bcancinov/mdc-power-p6/sim/p6.asc

@1: fra; delay=1m fstart=1.875K fend=480K oct=2 fcoarse=15K pp0=192m pp1=12m f0=1.875K f1=30K tavgmin=50µ tsettle=33.3333µ
C1: cap; 0.1µ
C2: cap; 1µF
C3: cap; 22µ; Rser=40m Lser=1.7n
C4: cap; 100µ; Rser=80m Lser=3n
C5: cap; 10µ; Rser=3m Lser=0.5n
Coc1: cap; 39.162µ; x4; Rser=2.17m Lser=0.2n
Cth1: cap; 10n
Cthp1: cap; 180p
E1: e; 1
E2: e; 1
R1: res; 10.7k
R2: res; 1k
R3: res; 100k
R4: res; '6/0.01'
R5: res; 0.5
R6: res; 0.22
R7: res; '6/3'
Rfreq1: res; 47k
Riset1: res; 60.4k
Rth1: res; 1.33k
U1: LT8624S
U2: XGL4020
U3: XGL4020
Vin1: voltage; 12V
Named nets: 0, SW, PGFB, SET, VOUT1, VLDO, out1, out2
LT8624S - 18V, 4A Synchronous Step-Down Silent Switcher with Ultralow Noise Reference
.tran 5m startup
.fra startup
*.options plotwinsize = 0
7.19pF Cpar
